josko7452/actidamp-mk4-smd/ltspice/full_actidamp.asc

C1: cap; 470p
C2: cap; 100p
C3: cap; 1µ
C4: cap; 680p
C5: cap; 680p
C6: cap; 100p
C7: cap; 1µ
C8: cap; 300p
C9: cap; 15p
C10: cap; 15p
C11: cap; 470n
C12: cap; 470n
C13: cap; 470n
C14: cap; 587n
C15: cap; 2.2n
C16: cap; 15n
C17: cap; 680n
C18: cap; 680n
C19: cap; 10000µ; 7.96µ
C20: cap; 3.18µ
C21: cap; 75n
E1: e; 1.0
E2: e; 1.0
E3: e; 1.0
I1: current; SINE(0 1.0111 1000); AC 1.0111
J1: njf; LSK389C
J2: njf; LSK389C
L1: ind; 220µ
R1: res; 3300
R2: res; 1800
R3: res; 1800
R4: res; 47
R5: res; 3.3k
R6: res; 100
R7: res; 1.6Meg
R8: res; 12k
R9: res; 10k
R10: res; 12k
R11: res; 1Meg
R12: res; 10k
R13: res; 1.6Meg
R14: res; 5.1k
R15: res; 220
R16: res; 51k
R17: res; 12k
R18: res; 4k7
R19: res; 82k
R20: res; 4.87k
R21: res; 542
R22: res; 3.3k
R23: res; 390
R24: res; 6.8k
R25: res; 5k
R26: res; 750
R27: res; 1k
R28: res; 100
R29: res; 500
R30: res; 1Meg
R31: res; 1Meg
R32: res; 10Gig
R33: res; 1k
R34: res; 1k
R35: res; 111.11
R36: res; 1k
R37: res; 1
U1: opamp2; NE5532
U2: opamp2; LF411C
U3: opamp2; NE5532
U4: opamp2; NE5532
U5: opamp2; NE5532
U6: opamp2; LF411C
U7: opamp2; NE5532
V2: voltage; 18
V3: voltage; 18
Named nets: V_POS, V_NEG, 0, V_TEST
.lib ne5534.sub
.lib lf411.sub
* LSK389C       November 29, 2010
.MODEL LSK389C NJF BETA=0.035 VTO=-0.54 LAMBDA=5.0E-3           
+ IS=3E-14 N= 1 RD=8 RS=7 CGD=5E-11 CGS=5E-11           
+ PB=1.2 FC=0.5 KF=0 AF=1
;.tran 0 3ms 2ms
.ac oct 1000 50 22000
