josko7452/actidamp-mk4-smd/ltspice/psu_actidamp.asc

C1: cap; 220µ
C2: cap; 100n
C3: cap; 100n
C4: cap; 10µ
Q1: npn; BC846B
R1: res; 220
R2: res; 10
R3: res; 2200
R_Load: res; 500
V1: voltage; 18.5
Named nets: 0
.tran 10ms
